Sandman1234/AirProps/Bomb/_readMe_datas/schematicwoutPU.kicad_sch

## KiCad design Bomb/_readMe_datas/schematicwoutPU.kicad_sch (2026-10-06)

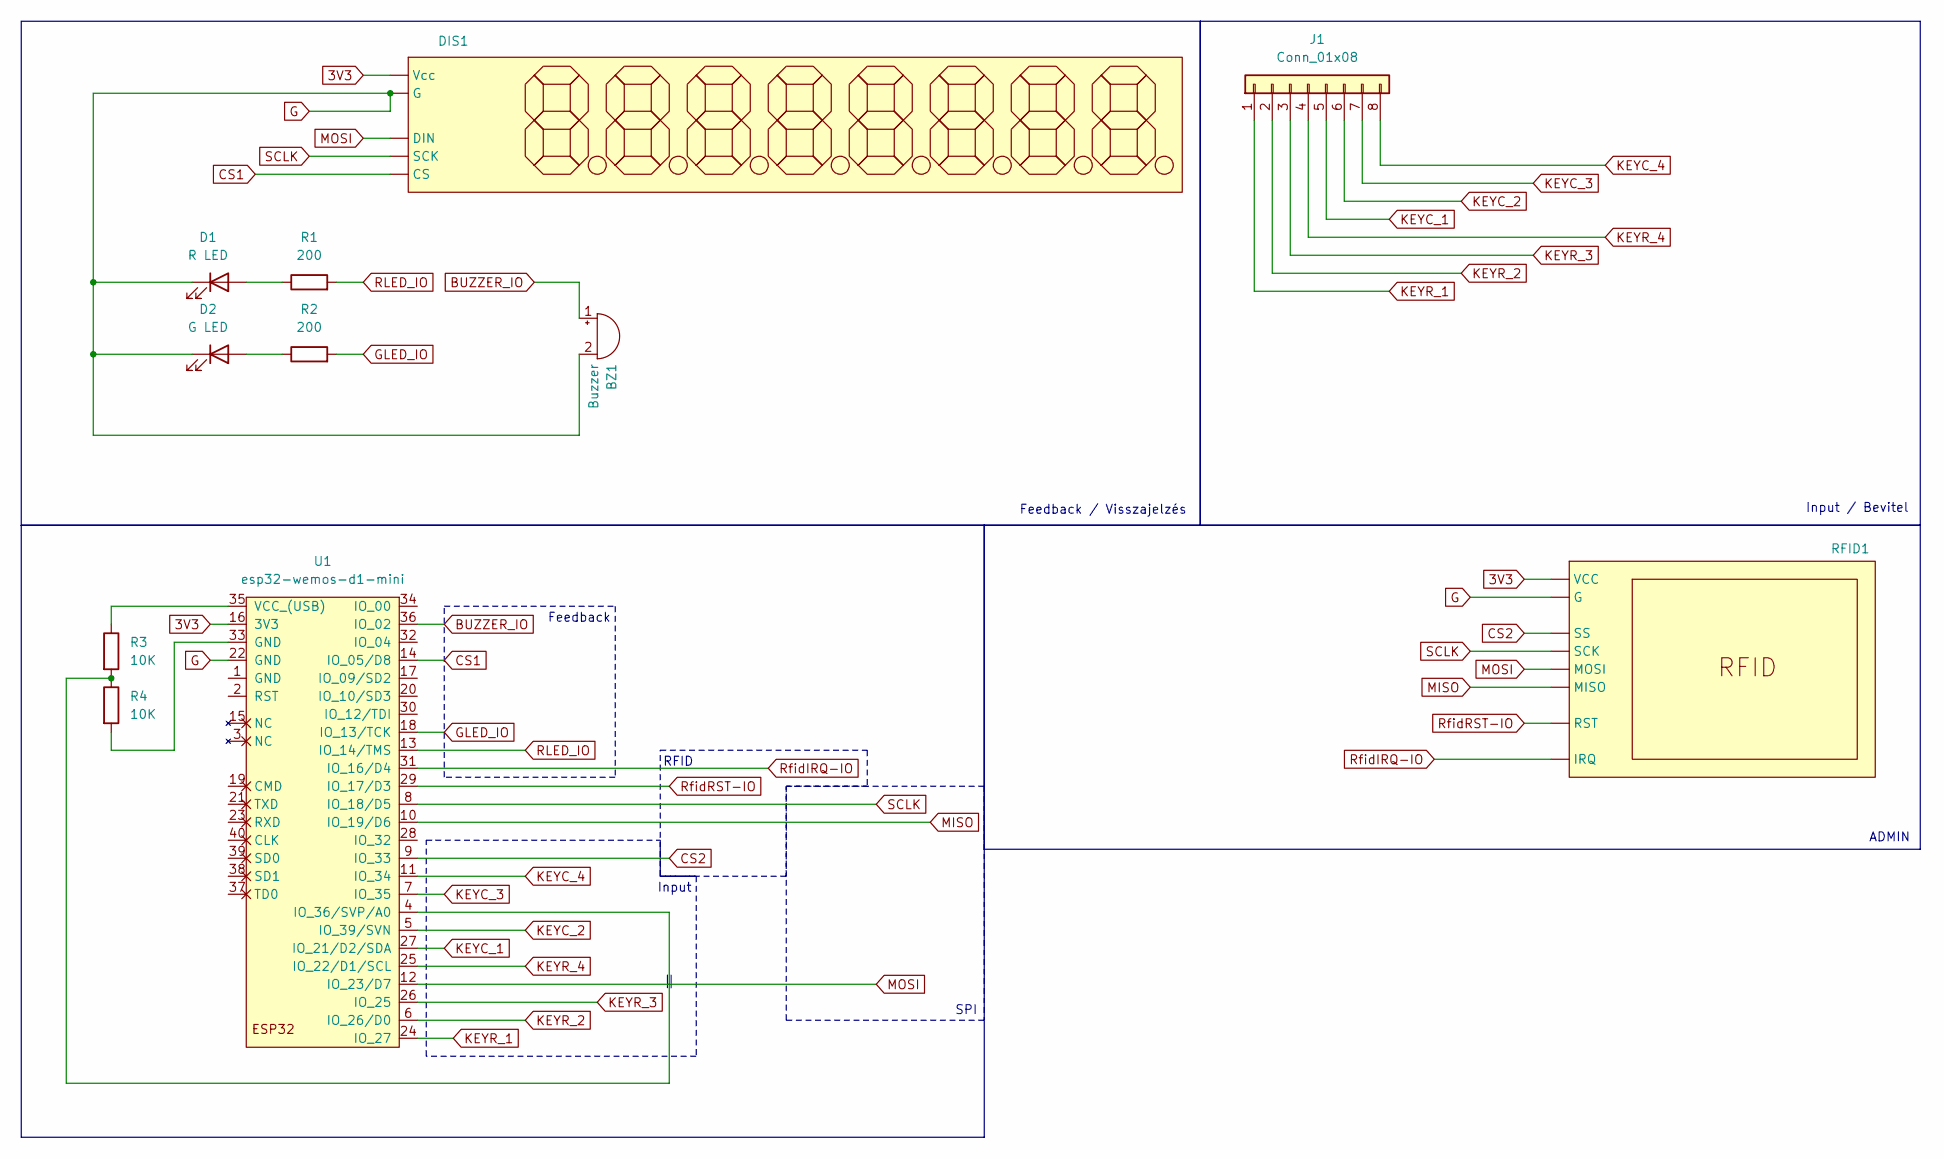
[picture p8: schematic schematicwoutPU.kicad_sch]

Parts:
BZ1: Buzzer
D1: R LED
D2: G LED
DIS1: (no value)
J1: Conn_01x08
R1, R2: 200
R3, R4: 10K
RFID1: (no value)
U1: esp32-wemos-d1-mini

Connections:
3V3: DIS1., RFID1., U1.16 (3V3)
BUZZER_IO: BZ1.1 (+), U1.36 (IO_02)
CS1: DIS1., U1.14 (IO_05/D8)
CS2: RFID1., U1.9 (IO_33)
G: BZ1.2 (-), D1.1 (K), D2.1 (K), DIS1., RFID1., U1.22 (GND)
GLED_IO: R2.2, U1.18 (IO_13/TCK)
KEYC_1: J1.5, U1.27 (IO_21/D2/SDA)
KEYC_2: J1.6, U1.5 (IO_39/SVN)
KEYC_3: J1.7, U1.7 (IO_35)
KEYC_4: J1.8, U1.11 (IO_34)
KEYR_1: J1.1, U1.24 (IO_27)
KEYR_2: J1.2, U1.6 (IO_26/D0)
KEYR_3: J1.3, U1.26 (IO_25)
KEYR_4: J1.4, U1.25 (IO_22/D1/SCL)
MISO: RFID1., U1.10 (IO_19/D6)
MOSI: DIS1., RFID1., U1.12 (IO_23/D7)
unnamed: D1.2 (A), R1.1
unnamed: D2.2 (A), R2.1
unnamed: R3.1, U1.35 (VCC_(USB))
unnamed: R3.2, R4.1, U1.4 (IO_36/SVP/A0)
unnamed: R4.2, U1.33 (GND)
RLED_IO: R1.2, U1.13 (IO_14/TMS)
RfidIRQ-IO: RFID1., U1.31 (IO_16/D4)
RfidRST-IO: RFID1., U1.29 (IO_17/D3)
SCLK: DIS1., RFID1., U1.8 (IO_18/D5)

Notes on the sheet:
Feedback
Input
Input / Bevitel
RFID
ADMIN
Feedback / Visszajelzés
SPI
